CrackberryPi/hardware/Eagle/59440996.jpg

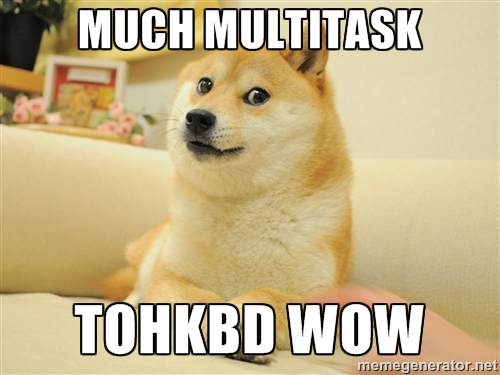
Eagle/59440996.jpg
