CrackberryPi/hardware/images/fotos/20150325_001.jpg

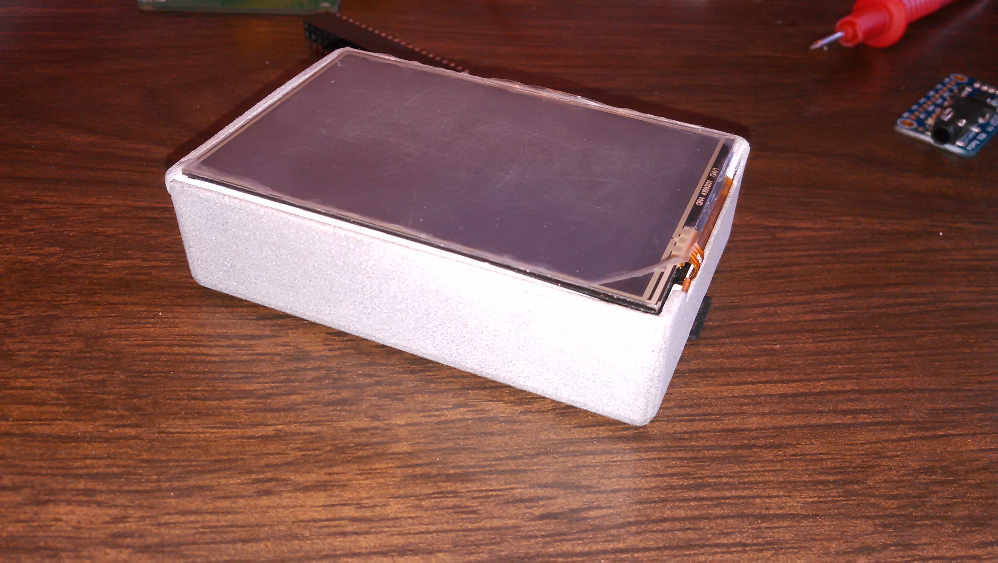
images/fotos/20150325_001.jpg
