CrackberryPi/hardware/images/fotos/20150325_002.jpg

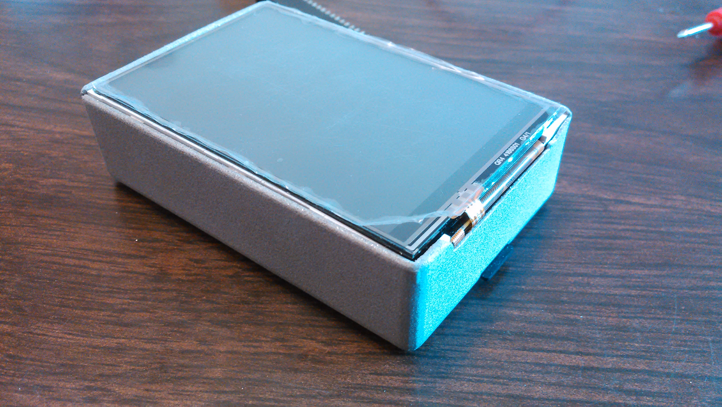
images/fotos/20150325_002.jpg
