CrackberryPi/hardware/images/fotos/20150325_003.jpg

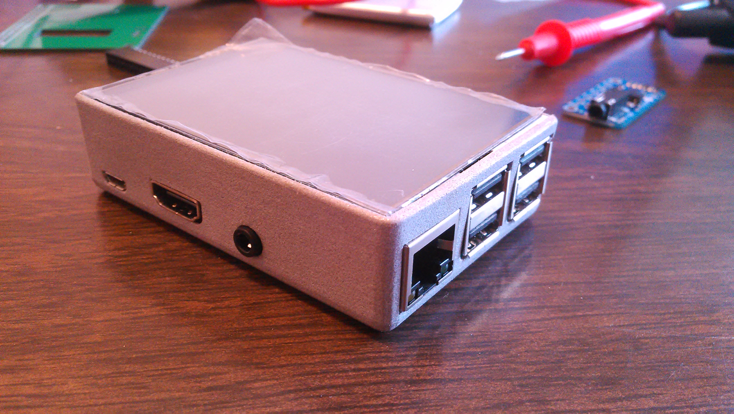
images/fotos/20150325_003.jpg
