CrackberryPi/hardware/images/fotos/20150325_004.jpg

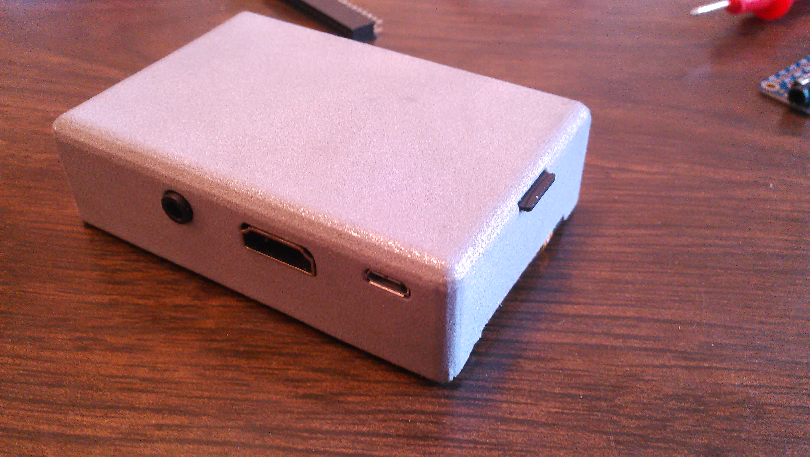
images/fotos/20150325_004.jpg
