CrackberryPi/hardware/images/fotos/20150325_005.jpg

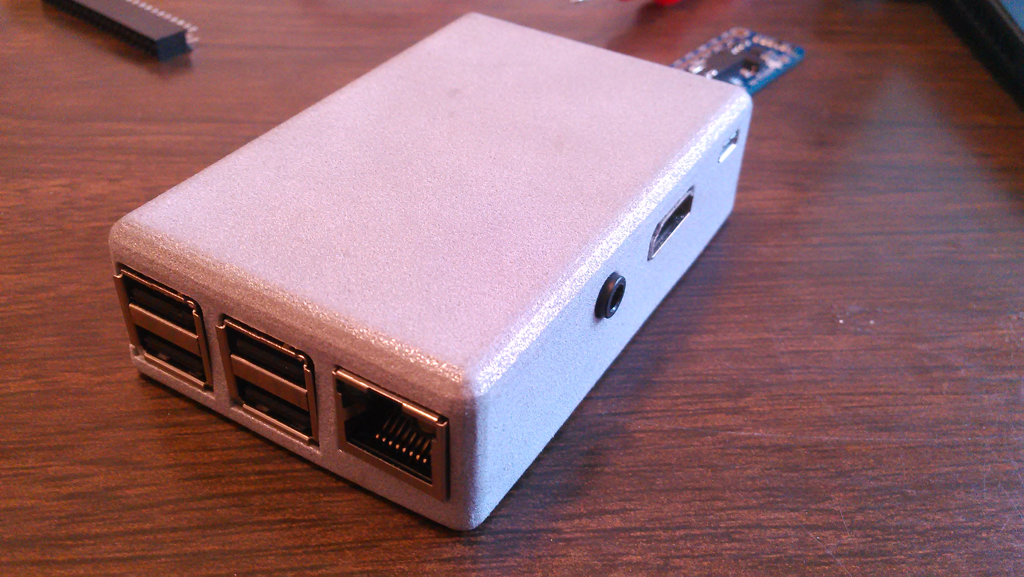
images/fotos/20150325_005.jpg
