CrackberryPi/hardware/images/fotos/20150325_006.jpg

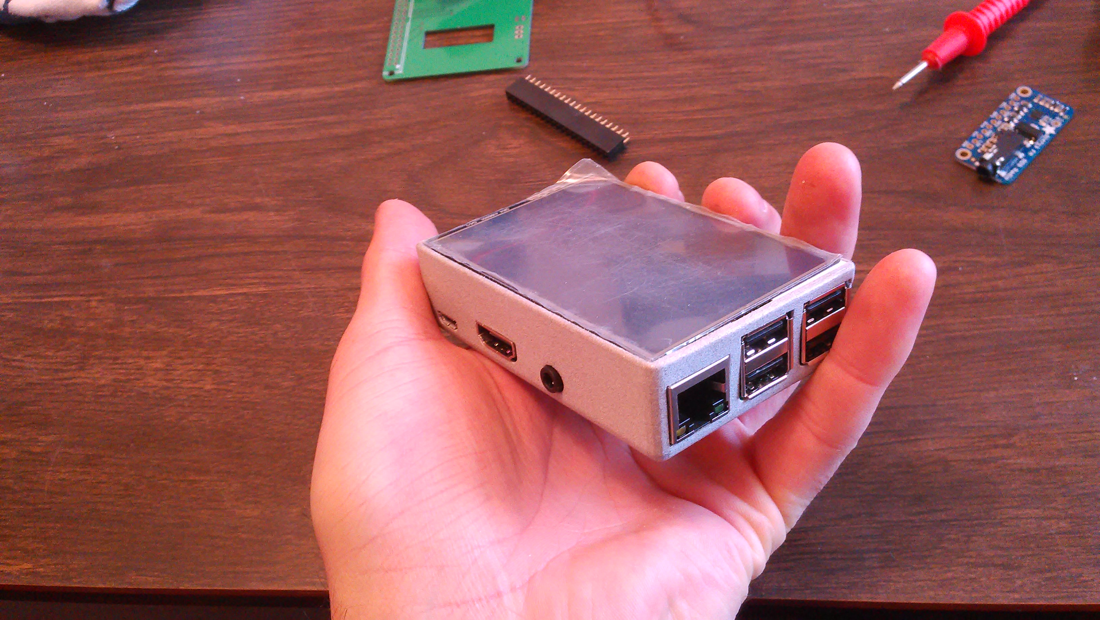
images/fotos/20150325_006.jpg
