CrackberryPi/hardware/images/fotos/20150325_007.jpg

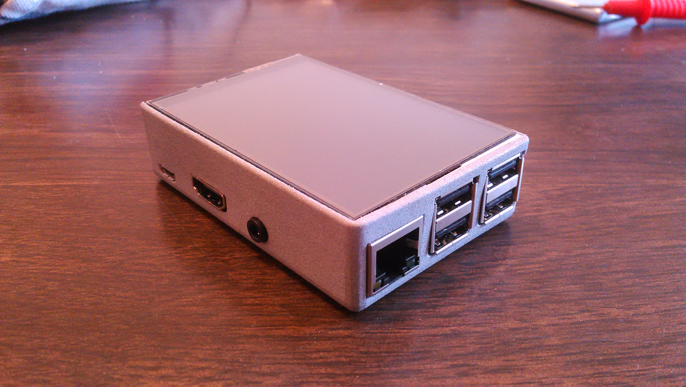
images/fotos/20150325_007.jpg
