CrackberryPi/hardware/images/fotos/20150325_008.jpg

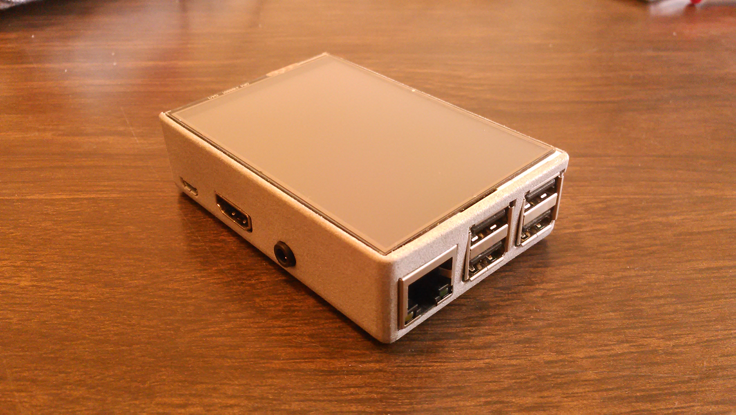
images/fotos/20150325_008.jpg
