CrackberryPi/hardware/images/fotos/20150325_009.jpg

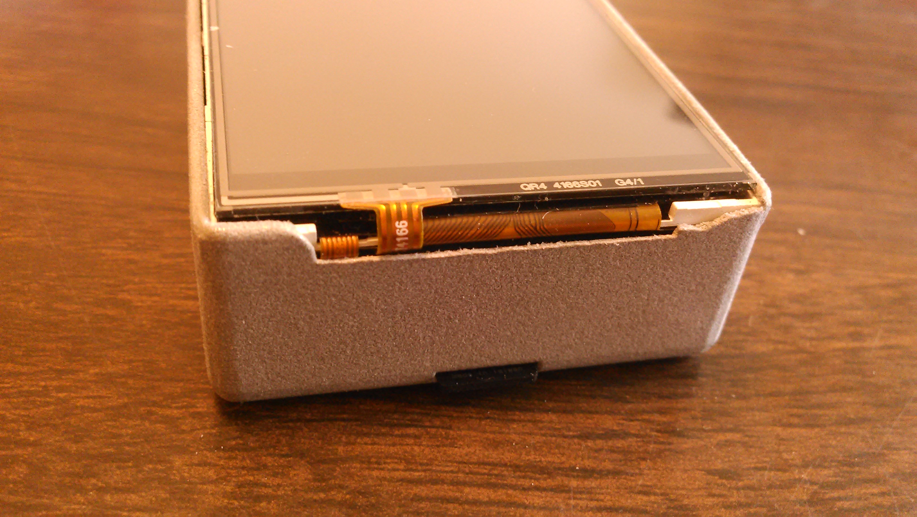
images/fotos/20150325_009.jpg
