CrackberryPi/hardware/images/kbd.jpg

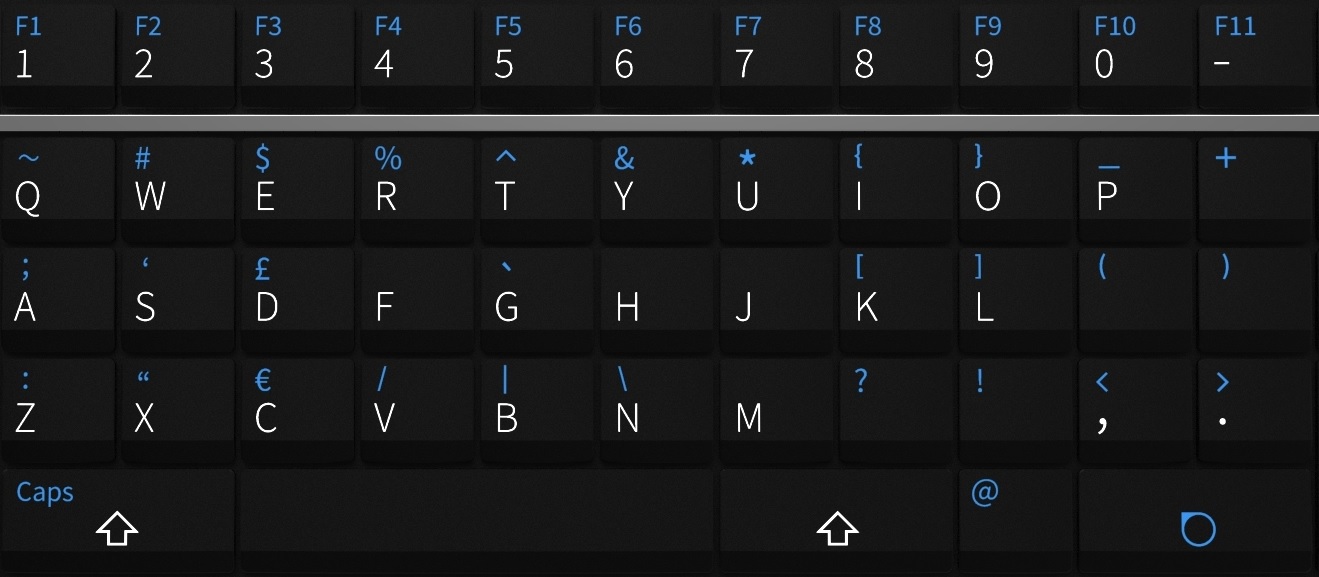
images/kbd.jpg
