CrackberryPi/hardware/images/raspbian.jpg

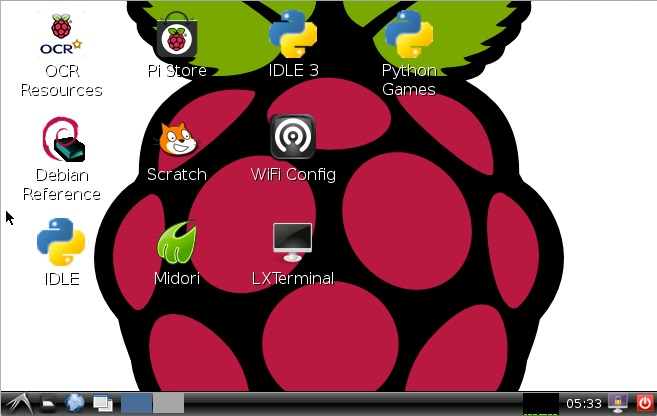
images/raspbian.jpg
