CrackberryPi/hardware/Eagle/CrackberryPi_1.0.5.brd

## EAGLE design Eagle/CrackberryPi_1.0.5.brd (2015-04-28)

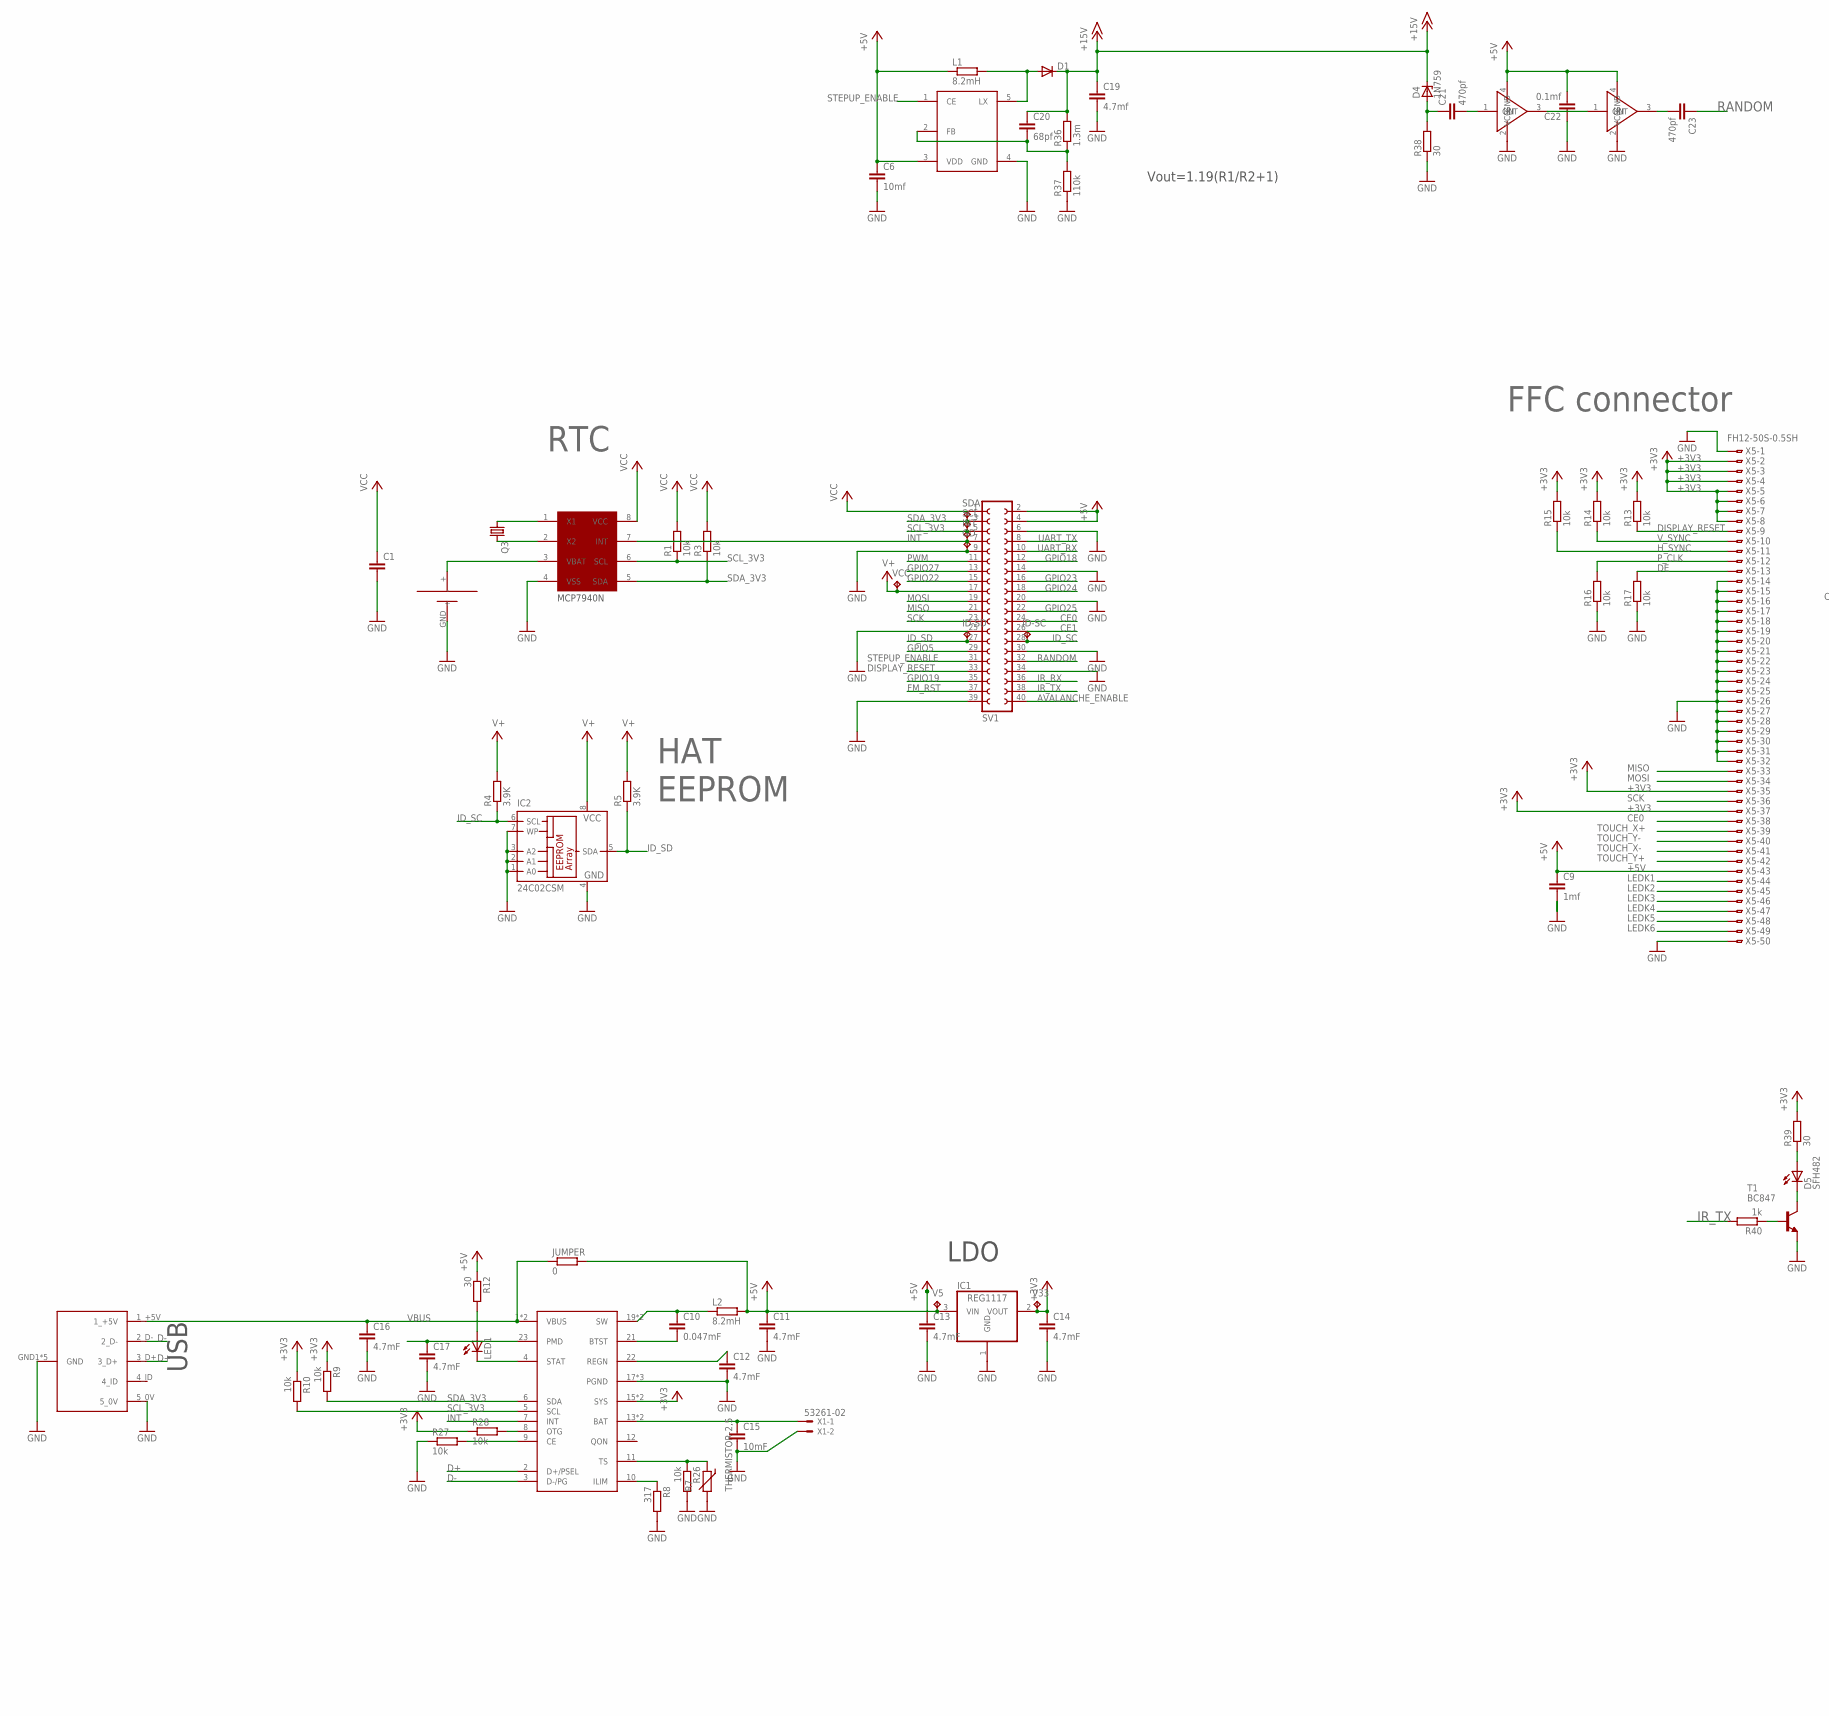
[picture p51: schematic CrackberryPi_1.0.5.sch, part in row 1, column 1]

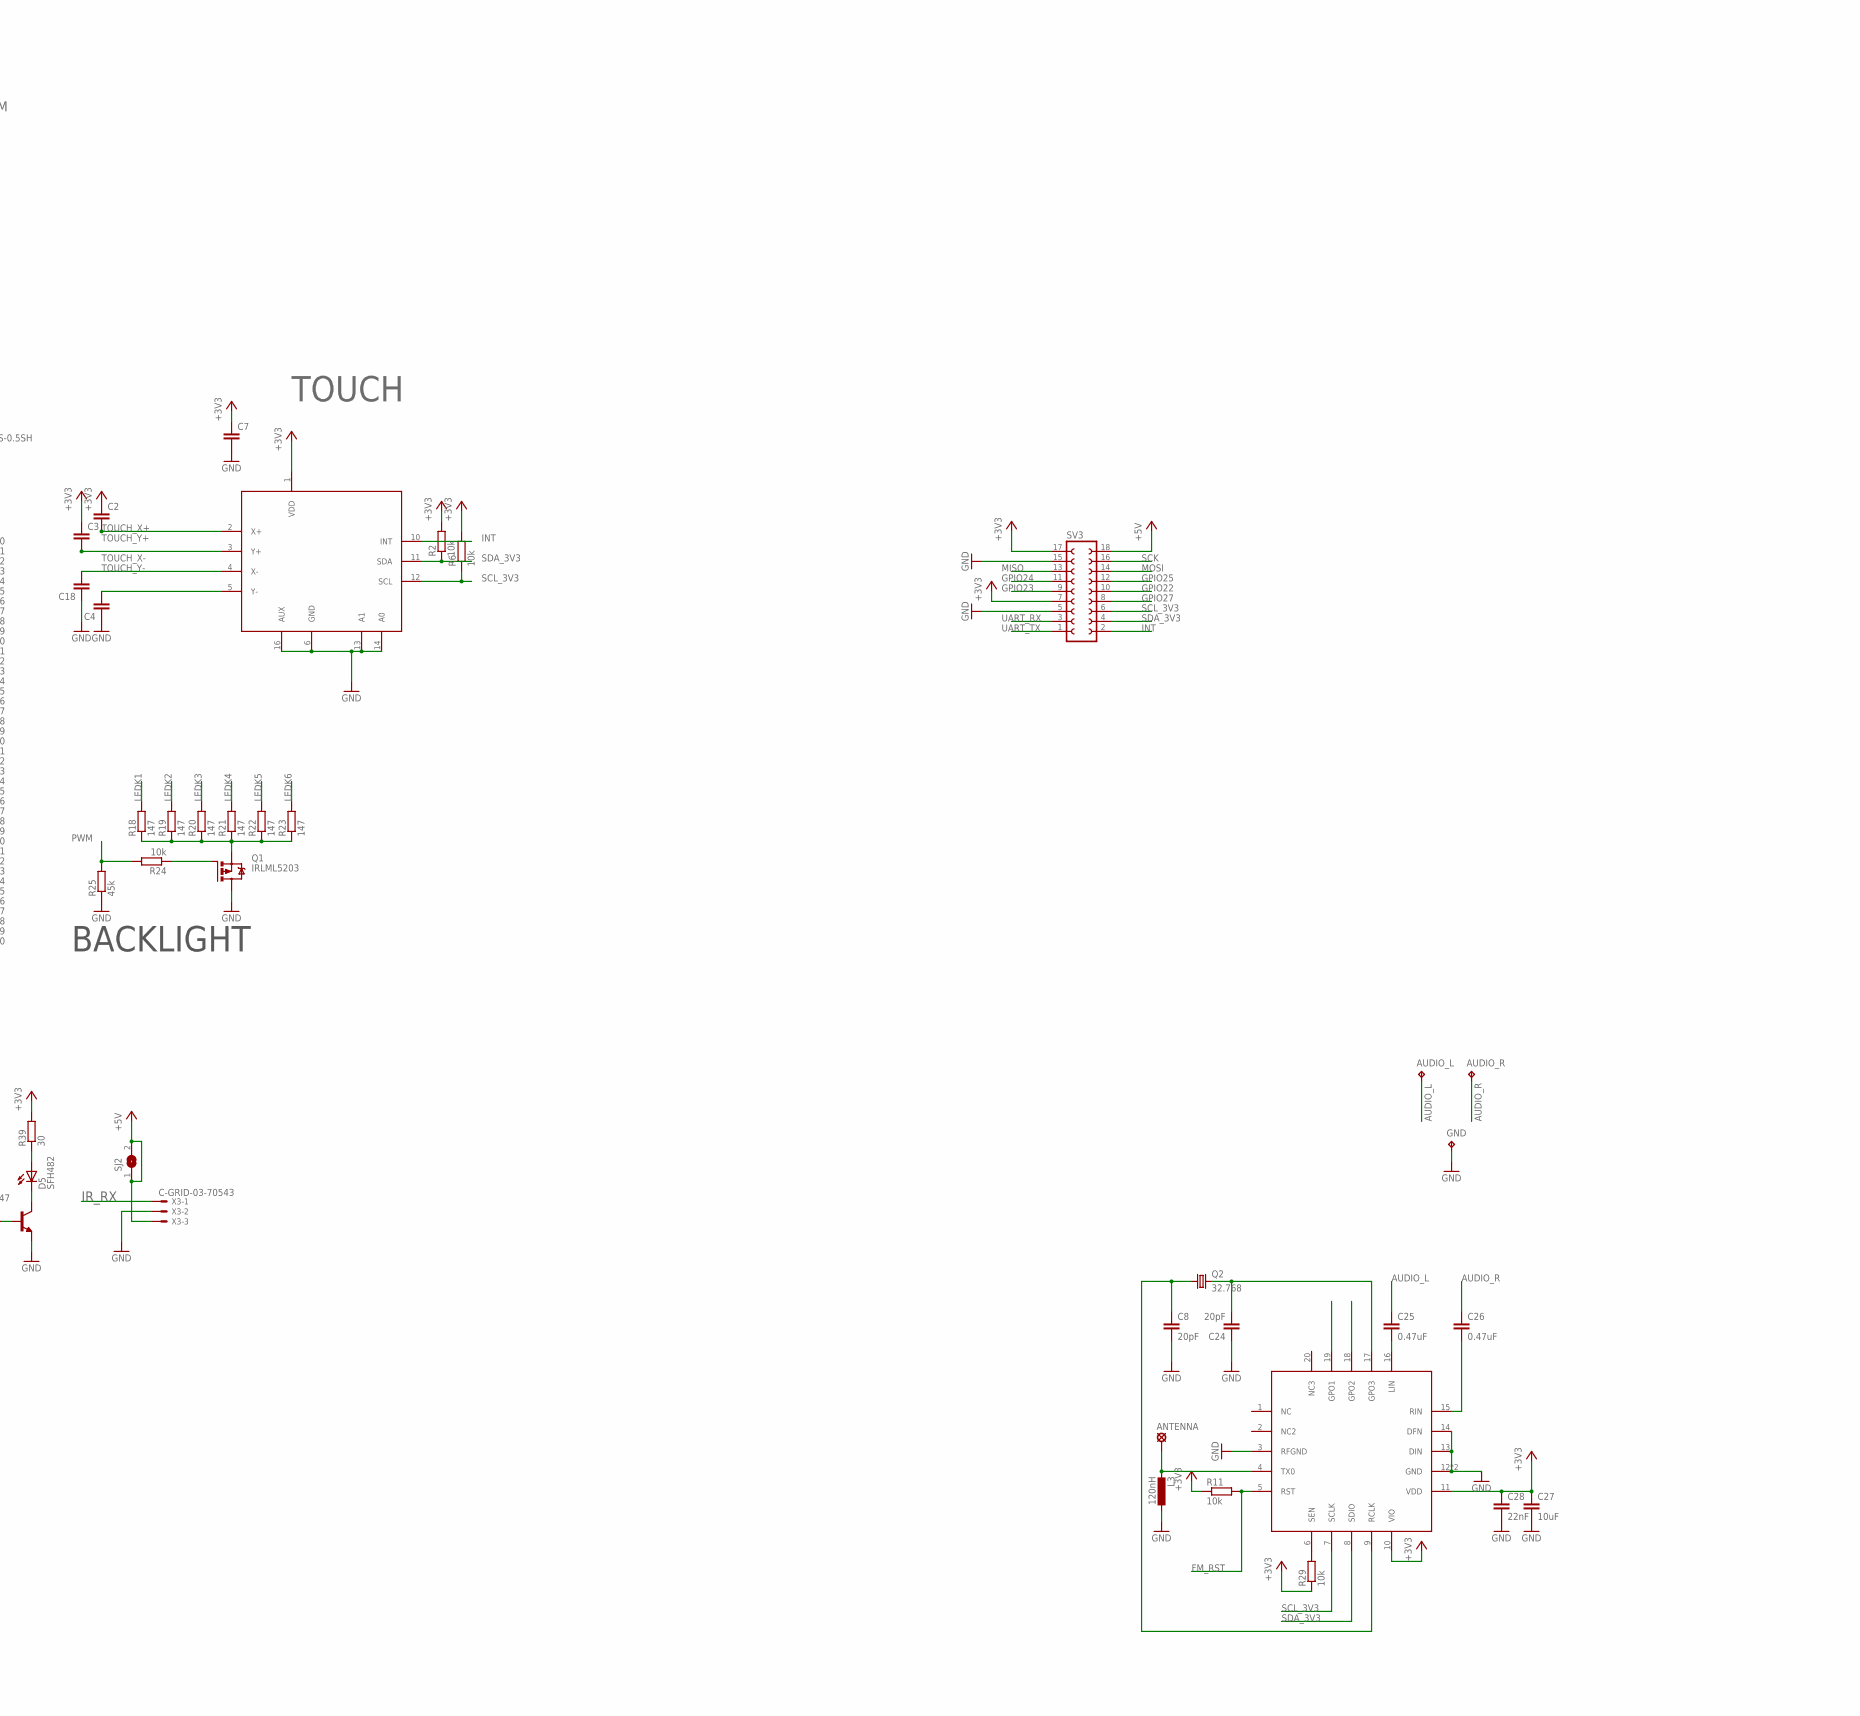
[picture p52: schematic CrackberryPi_1.0.5.sch, part in row 1, column 2]

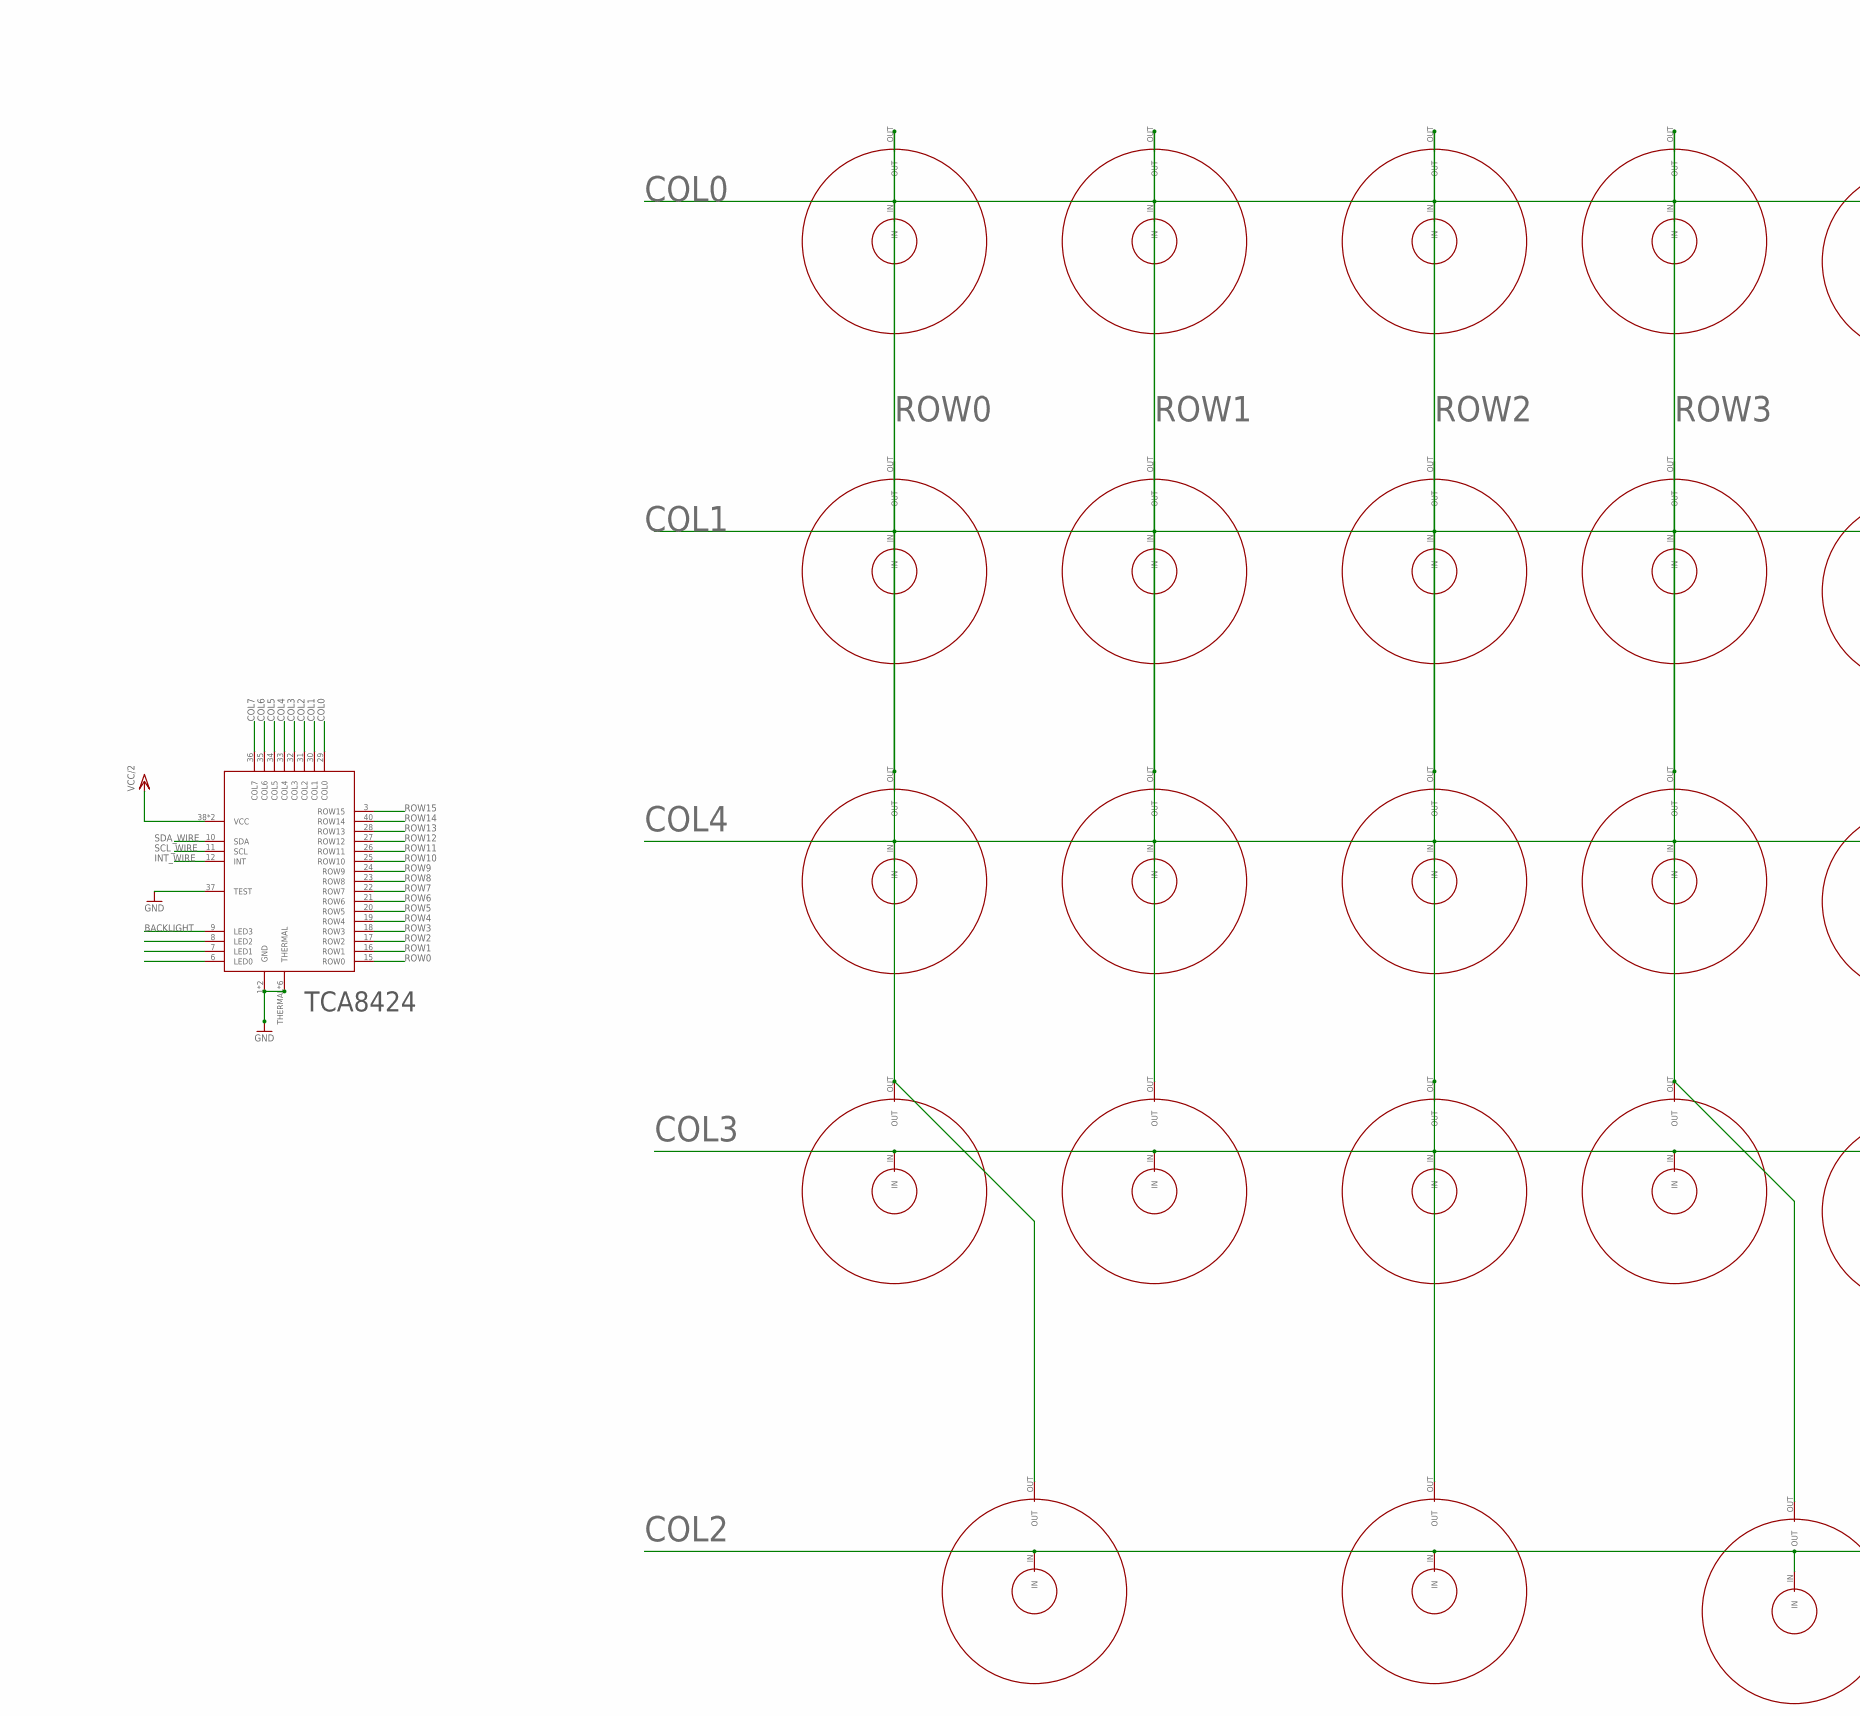
[picture p53: schematic CrackberryPi_1.0.5.sch, part in row 1, column 3]

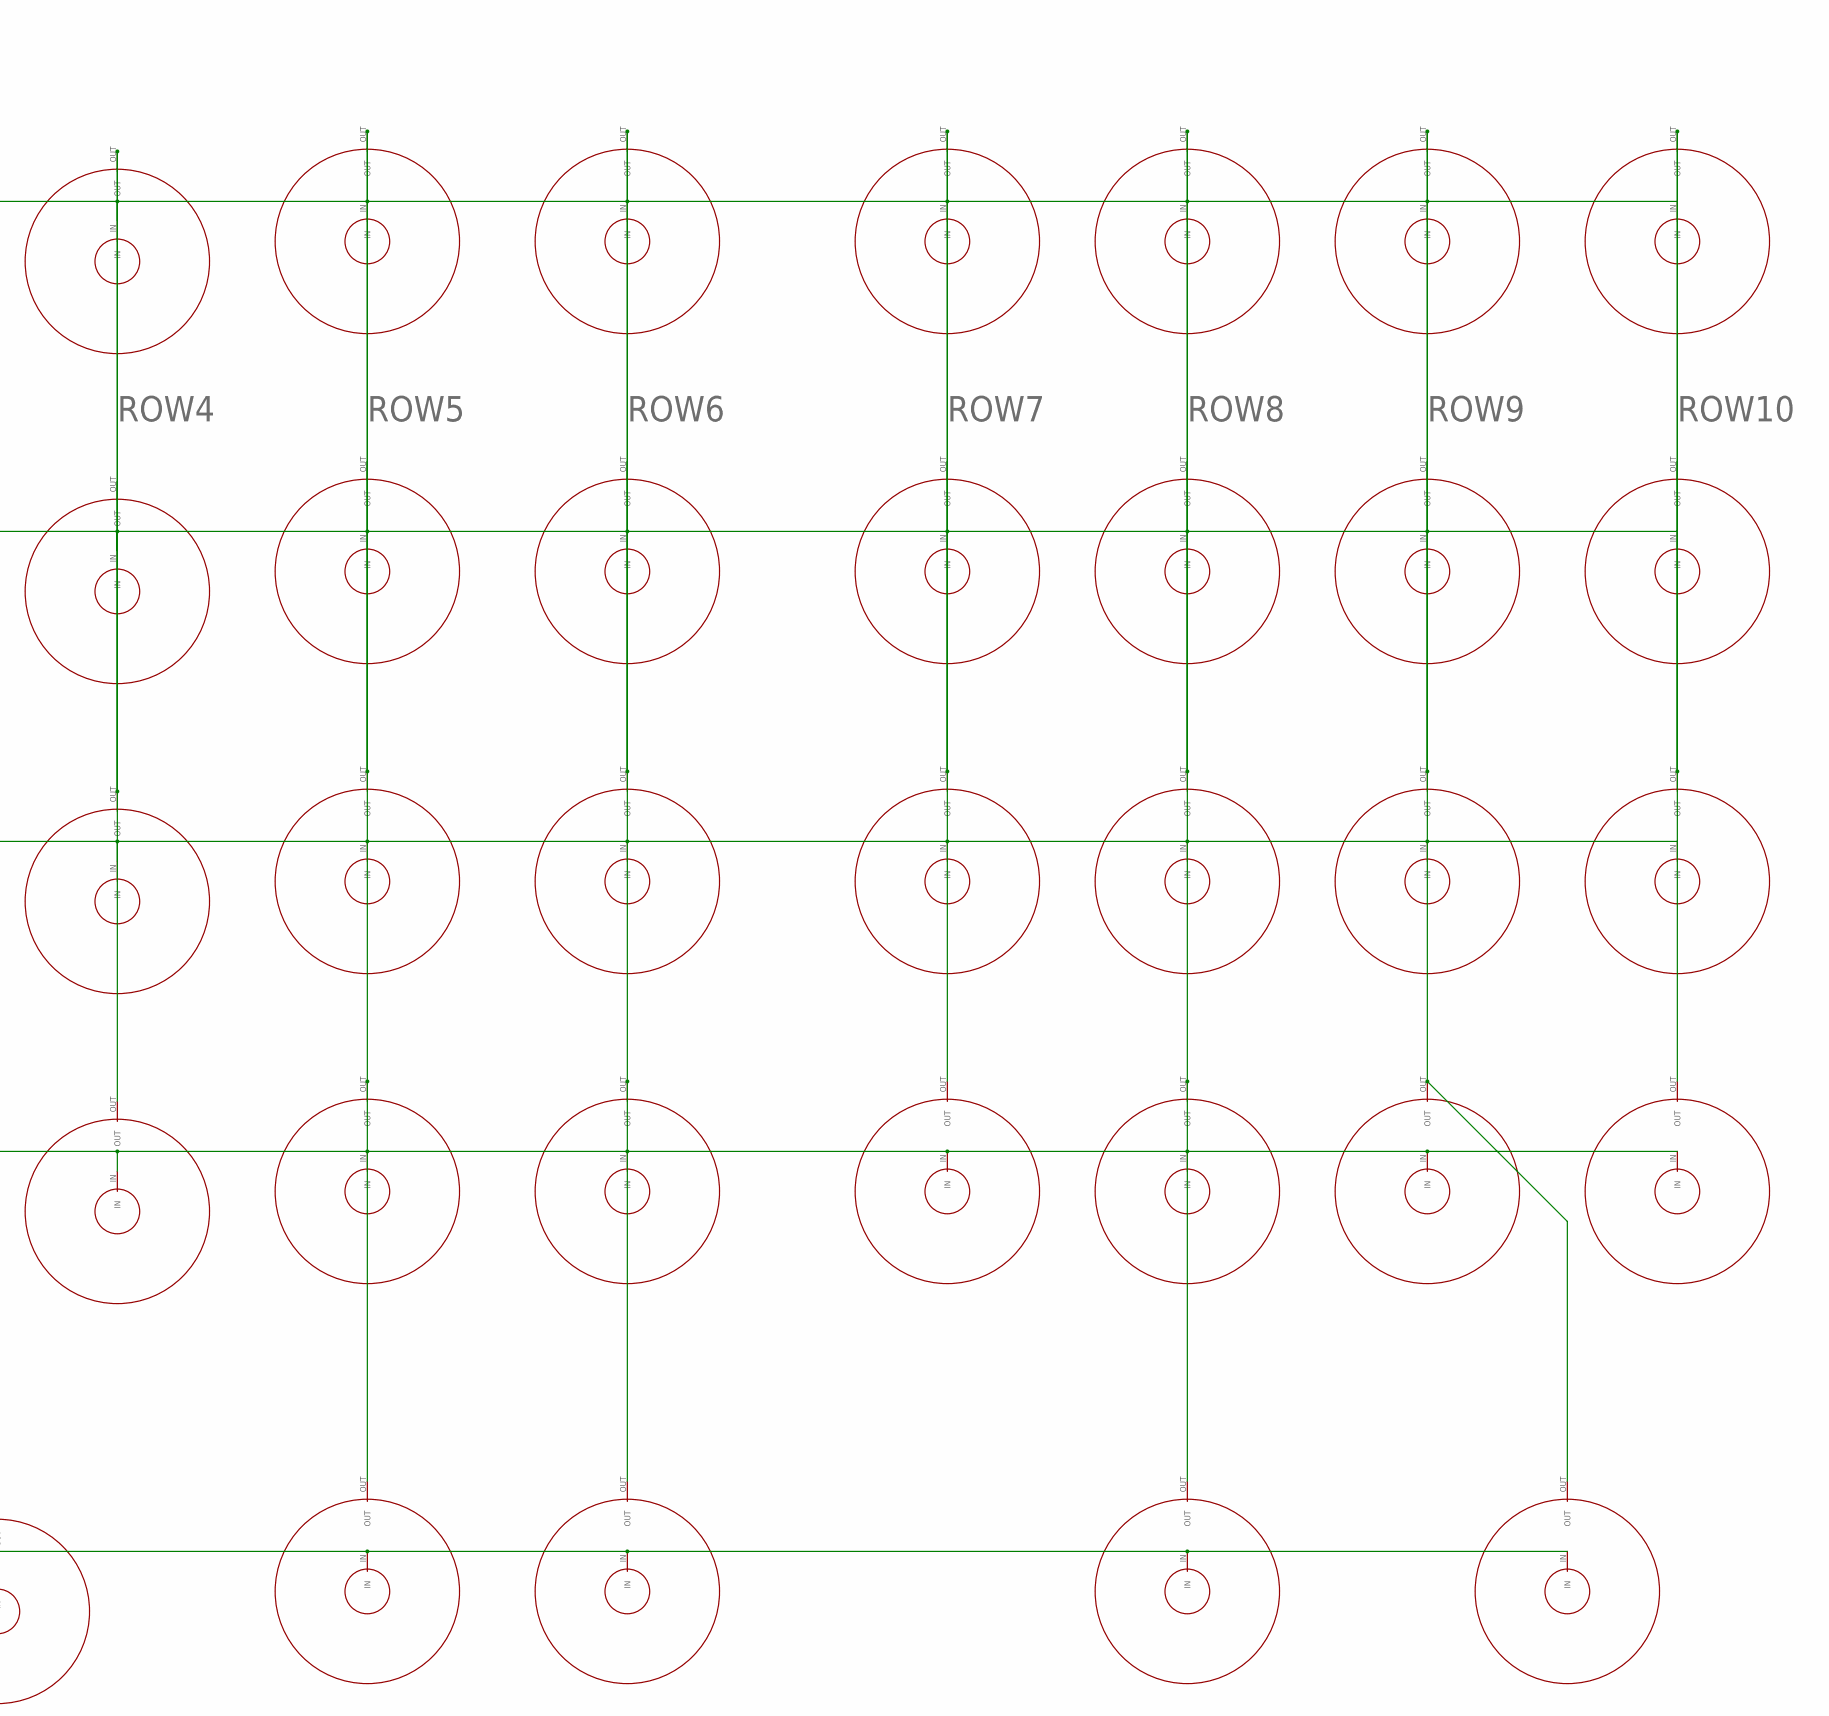
[picture p54: schematic CrackberryPi_1.0.5.sch, part in row 1, column 4]

Parts:
0, 1, 2, 3, 4, 5, 6, 7, 8, 9, .: DOME; 4MM
!: DOME; 4MM
(: DOME; 4MM
): DOME; 4MM
+: DOME; 4MM
,: DOME; 4MM
-: DOME; 4MM
?: DOME; 4MM
@: DOME; 4MM
A: DOME; 4MM
ANTENNA: LSP10
AUDIO_L: TPB2,54; B2,54
AUDIO_R: TPB2,54; B2,54
B: DOME; 4MM
C: DOME; 4MM
C1, C2, C3, C4, C7, C18: C-EUC0603; C0603
C6: 10mf; C0603
C8, C24: 20pF; C0603
C9: 1mf; C0603
C10: 0.047mF; C0402
C11, C12, C13, C14, C16, C17: 4.7mF; C0603
C15: 10mF; C1206
C19: 4.7mf; C0603
C20: 68pf; C0603
C21, C23: 470pf; C0603
C22: 0.1mf; C0603
C25, C26: 0.47uF; C0603
C27: 10uF; C0603
C28: 22nF; C0603
D: DOME; 4MM
D1: DIODE-SOD123; SOD123
D4: 1N759; SOD80C
D5: SFH482
E: DOME; 4MM
F: DOME; 4MM
FN-RIGHT: DOME; 4MM
G: DOME; 4MM
GD: TPB1,27; B1,27
GND: TPB2,54; B2,54
H: DOME; 4MM
I: DOME; 4MM
IC1: REG1117; SOT223
IC2: 24C02CSM; SO-08M
ID-SC: TPB1,27; B1,27
ID-SD: TPB1,27; B1,27
INT: TPB1,27; B1,27
J: DOME; 4MM
JUMPER: 0; R1206
K: DOME; 4MM
L: DOME; 4MM
L1: 8.2mH; R0805
L2: 8.2mH; R1206W
L3: 120nH; L2012C
LED1: LEDSML0603; SML0603
M: DOME; 4MM
N: DOME; 4MM
O: DOME; 4MM
P: DOME; 4MM
Q: DOME; 4MM
Q1: IRLML5203; MICRO3
Q2: 32.768; MM20SS
Q3: CRYSTALMM20SS; MM20SS
R: DOME; 4MM
R1, R2, R3, R6, R9, R10, R11, R13, R14, R15, R16, R17, R24, R26, R27, R28, R29: 10k; R0603
R4, R5: 3.9K; R0603
R7: THERMISTOR-2,5; RS-2,5
R8: 317; R0603
R12, R38, R39: 30; R0603
R18, R19, R20, R21, R22, R23: 147; R0603
R25: 45k; R0603
R36: 1.3m; R0603
R37: 110k; R0603
R40: 1k; R0603
S: DOME; 4MM
SCL: TPB1,27; B1,27
SDA: TPB1,27; B1,27
SHIFT-RIGHT: DOME; 4MM
SHILFT-LEFT: DOME; 4MM
SJ2: SJ
SPACE1, SPACE2, SPACE3: DOME; 4MM
SV1: FE20-2
SV3: FE09-2
T: DOME; 4MM
T1: BC847; SOT23
U: DOME; 4MM
U$1: BQ24297; VQFN-4X4-24
U$2: NCP1406; SOT23-5L
U$3, U$10: MAX2650; SOT143-W
U$4: CR1216
U$5: MCP7940N; SO08
U$6: TSC2007; TSSOP16
U$7: TCA8424; QFN40
U$8: SI4713; QFN20-3X3
U$9: MICRO_USB
V: DOME; 4MM
V5, V33: TPB1,27; B1,27
VCC: TPB1,27; B1,27
W: DOME; 4MM
X: DOME; 4MM
X1: 53261-02
X3: C-GRID-03-70543; 70543-03
X5: FH12-50S-0.5SH
Y: DOME; 4MM
Z: DOME; 4MM

Connections:
+3V3: C2.1, C3.1, C7.1, C14.1, C27.1, C28.1, IC1.2 (VOUT), R2.2, R6.2, R9.1, R10.1, R11.1, R13.2, R14.2, R15.2, R28.1, R29.1, R39.2, SV3.7, SV3.17, U$1.15 (SYS), U$1.16 (SYS), U$6.1 (VDD), U$8.10 (VIO), U$8.11 (VDD), V33.TP, X5.2, X5.3, X5.4, X5.5, X5.6, X5.7, X5.8, X5.35, X5.37
+5V: C6.1, C9.1, C11.1, C13.1, C22.2, IC1.3 (VIN), JUMPER.2, L1.1, L2.2, R12.1, SJ2.1, SJ2.2, SV1.2, SV1.4, SV3.18, U$2.3 (VDD), U$3.4 (VCC), U$10.4 (VCC), V5.TP, X3.3, X5.43
+15V: C19.1, C20.1, D1.C, D4.C, R36.2
AUDIO_L: AUDIO_L.TP, C25.1
AUDIO_R: AUDIO_R.TP, C26.1
AVALANCHE_ENABLE: SV1.40
BACKLIGHT: U$7.9 (LED3)
BASE: R40.1, T1.1 (B)
CE0: SV1.24, X5.38
CE1: SV1.26
COL0: 0.IN, 1.IN, 2.IN, 3.IN, 4.IN, 5.IN, 6.IN, 7.IN, 8.IN, 9.IN, -.IN, U$7.29 (COL0)
COL1: +.IN, E.IN, I.IN, O.IN, P.IN, Q.IN, R.IN, T.IN, U.IN, U$7.30 (COL1), W.IN, Y.IN
COL2: @.IN, FN-RIGHT.IN, SHIFT-RIGHT.IN, SHILFT-LEFT.IN, SPACE1.IN, SPACE2.IN, SPACE3.IN, U$7.31 (COL2)
COL3: !.IN, ,.IN, ..IN, ?.IN, B.IN, C.IN, M.IN, N.IN, U$7.32 (COL3), V.IN, X.IN, Z.IN
COL4: (.IN, ).IN, A.IN, D.IN, F.IN, G.IN, H.IN, J.IN, K.IN, L.IN, S.IN, U$7.33 (COL4)
COL5: U$7.34 (COL5)
COL6: U$7.35 (COL6)
COL7: U$7.36 (COL7)
COLLECTOR: D5.K (C), T1.3 (C)
D+: U$1.2 (D+/PSEL), U$9.3_D+
D-: U$1.3 (D-/PG), U$9.2_D-
DE: R17.2, X5.13
DISPLAY_RESET: R13.1, SV1.33, X5.9
EMITTER: T1.2 (E)
FB: C20.2, R36.1, R37.2, U$2.2 (FB)
FM_RST: R11.2, SV1.37, U$8.5 (RST)
GND: C1.2, C4.1, C6.2, C7.2, C8.2, C9.2, C11.2, C12.2, C13.2, C14.2, C15.2, C16.2, C17.2, C18.1, C19.2, C22.1, C24.1, C27.2, C28.2, GD.TP, GND.TP, IC1.1 (GND), IC2.1 (A0), IC2.2 (A1), IC2.3 (A2), IC2.4 (GND), IC2.7 (WP), L3.1, Q1.3 (D), R7.2, R8.2, R16.1, R17.1, R25.1, R26.2, R27.1, R37.1, R38.1, SV1.6, SV1.9, SV1.14, SV1.20, SV1.25, SV1.30, SV1.34, SV1.39, SV3.5, SV3.15, U$1.17 (PGND), U$1.18 (PGND), U$1.P$1 (PGND), U$2.4 (GND), U$3.2 (GND), U$4.GND (-), U$5.4 (VSS), U$6.6 (GND), U$6.13 (A1), U$6.14 (A0), U$6.16 (AUX), U$7.1 (GND), U$7.4 (GND), U$7.37 (TEST), U$7.THERMAL, U$7.VIA1 (THERMAL), U$7.VIA2 (THERMAL), U$7.VIA3 (THERMAL), U$7.VIA4 (THERMAL), U$7.VIA5 (THERMAL), U$8.3 (RFGND), U$8.12 (GND), U$8.13 (DIN), U$8.14 (DFN), U$8.P$1 (GND), U$9.5_0V, U$9.GND1 (GND), U$9.GND2 (GND), U$9.GND5 (GND), U$9.P$1 (GND), U$9.P$7 (GND), U$10.2 (GND), X1.2, X3.2, X5.1, X5.14, X5.15, X5.16, X5.17, X5.18, X5.19, X5.20, X5.21, X5.22, X5.23, X5.24, X5.25, X5.26, X5.27, X5.28, X5.29, X5.30, X5.31, X5.32, X5.50
GPIO5: SV1.29
GPIO18: SV1.12
GPIO19: SV1.35
GPIO22: SV1.15, SV3.10
GPIO23: SV1.16, SV3.9
GPIO24: SV1.18, SV3.11
GPIO25: SV1.22, SV3.12
GPIO27: SV1.13, SV3.8
GPO1: U$8.19 (GPO1)
GPO2: U$8.18 (GPO2)
H_SYNC: R15.1, X5.11
ID_SC: IC2.6 (SCL), ID-SC.TP, R4.1, SV1.28
ID_SD: IC2.5 (SDA), ID-SD.TP, R5.1, SV1.27
INT: INT.TP, SV1.7, SV3.2, U$1.7 (INT), U$5.7 (INT), U$6.10 (INT)
INT_WIRE: U$7.12 (INT)
IN_1: C21.2, U$3.1 (IN)
IR_RX: SV1.36, X3.1
IR_TX: R40.2, SV1.38
LEDK1: R18.2, X5.44
LEDK2: R19.2, X5.45
LEDK3: R20.2, X5.46
LEDK4: R21.2, X5.47
LEDK5: R22.2, X5.48
LEDK6: R23.2, X5.49
LX: D1.A, L1.2, U$2.5 (LX)
MISO: SV1.21, SV3.13, X5.33
MOSI: SV1.19, SV3.14, X5.34
unnamed: C10.1, L2.1, U$1.19 (SW), U$1.20 (SW)
unnamed: C10.2, U$1.21 (BTST)
unnamed: C15.1, U$1.13 (BAT), U$1.14 (BAT), X1.1
unnamed: LED1.A, R12.2
unnamed: C12.1, U$1.22 (REGN)
unnamed: R7.1, R26.1, U$1.11 (TS)
unnamed: R8.1, U$1.10 (ILIM)
unnamed: C17.1, U$1.23 (PMD)
unnamed: LED1.C, U$1.4 (STAT)
unnamed: Q3.1, U$5.1 (X1)
unnamed: Q1.2 (S), R18.1, R19.1, R20.1, R21.1, R22.1, R23.1
unnamed: Q3.4 (2), U$5.2 (X2)
unnamed: R27.2, U$1.9 (CE)
unnamed: C21.1, D4.A, R38.2
unnamed: R28.2, U$1.8 (OTG)
unnamed: C24.2, Q2.4 (2), U$8.17 (GPO3)
unnamed: Q1.1 (G), R24.1
unnamed: C8.1, Q2.1, U$8.9 (RCLK)
unnamed: C25.2, U$8.16 (LIN)
unnamed: C26.2, U$8.15 (RIN)
unnamed: ANTENNA.MP, L3.2, U$8.4 (TX0)
unnamed: R29.2, U$8.6 (SEN)
unnamed: D5.A, R39.1
OUT1_IN2: U$3.3 (OUT), U$10.1 (IN)
OUT2: C23.2, U$10.3 (OUT)
PWM: R24.2, R25.2, SV1.11
P_CLK: R16.2, X5.12
RANDOM: C23.1, SV1.32
ROW0: 1.OUT, A.OUT, Q.OUT, SHILFT-LEFT.OUT, U$7.15 (ROW0), Z.OUT
ROW1: 2.OUT, S.OUT, U$7.16 (ROW1), W.OUT, X.OUT
ROW2: 3.OUT, C.OUT, D.OUT, E.OUT, SPACE1.OUT, U$7.17 (ROW2)
ROW3: 4.OUT, F.OUT, R.OUT, SPACE2.OUT, U$7.18 (ROW3), V.OUT
ROW4: 5.OUT, B.OUT, G.OUT, T.OUT, U$7.19 (ROW4)
ROW5: 6.OUT, H.OUT, N.OUT, SPACE3.OUT, U$7.20 (ROW5), Y.OUT
ROW6: 7.OUT, J.OUT, M.OUT, SHIFT-RIGHT.OUT, U.OUT, U$7.21 (ROW6)
ROW7: 8.OUT, ?.OUT, I.OUT, K.OUT, U$7.22 (ROW7)
ROW8: 9.OUT, !.OUT, @.OUT, L.OUT, O.OUT, U$7.23 (ROW8)
ROW9: 0.OUT, (.OUT, ,.OUT, FN-RIGHT.OUT, P.OUT, U$7.24 (ROW9)
ROW10: ).OUT, +.OUT, -.OUT, ..OUT, U$7.25 (ROW10)
ROW11: U$7.26 (ROW11)
ROW12: U$7.27 (ROW12)
ROW13: U$7.28 (ROW13)
ROW14: U$7.40 (ROW14)
ROW15: U$7.3 (ROW15)
SCK: SV1.23, SV3.16, X5.36
SCL_3V3: R1.1, R6.1, R10.2, SCL.TP, SV1.5, SV3.6, U$1.5 (SCL), U$5.6 (SCL), U$6.12 (SCL), U$8.7 (SCLK)
SCL_WIRE: U$7.11 (SCL)
SDA_3V3: R2.1, R3.1, R9.2, SDA.TP, SV1.3, SV3.4, U$1.6 (SDA), U$5.5 (SDA), U$6.11 (SDA), U$8.8 (SDIO)
SDA_WIRE: U$7.10 (SDA)
STEPUP_ENABLE: SV1.31, U$2.1 (CE)
TOUCH_X+: C2.2, U$6.2 (X+), X5.39
TOUCH_X-: C18.2, U$6.4 (X-), X5.41
TOUCH_Y+: C3.2, U$6.3 (Y+), X5.42
TOUCH_Y-: C4.2, U$6.5 (Y-), X5.40
UART_RX: SV1.10, SV3.3
UART_TX: SV1.8, SV3.1
V+: IC2.8 (VCC), R4.2, R5.2, SV1.17, VCC.TP
VBAT+: U$4.+, U$5.3 (VBAT)
VBUS: C16.1, JUMPER.1, U$1.1 (VBUS), U$1.24 (VBUS), U$9.1_+5V
VCC: C1.1, R1.2, R3.2, SV1.1, U$5.8 (VCC)
VCC/2: U$7.38 (VCC), U$7.39 (VCC)
V_SYNC: R14.1, X5.10

Notes on the sheet:
RTC
HAT EEPROM
TOUCH
FFC connector
BACKLIGHT
MCP7940N
USB
LDO
Vout=1.19(R1/R2+1)
TCA8424

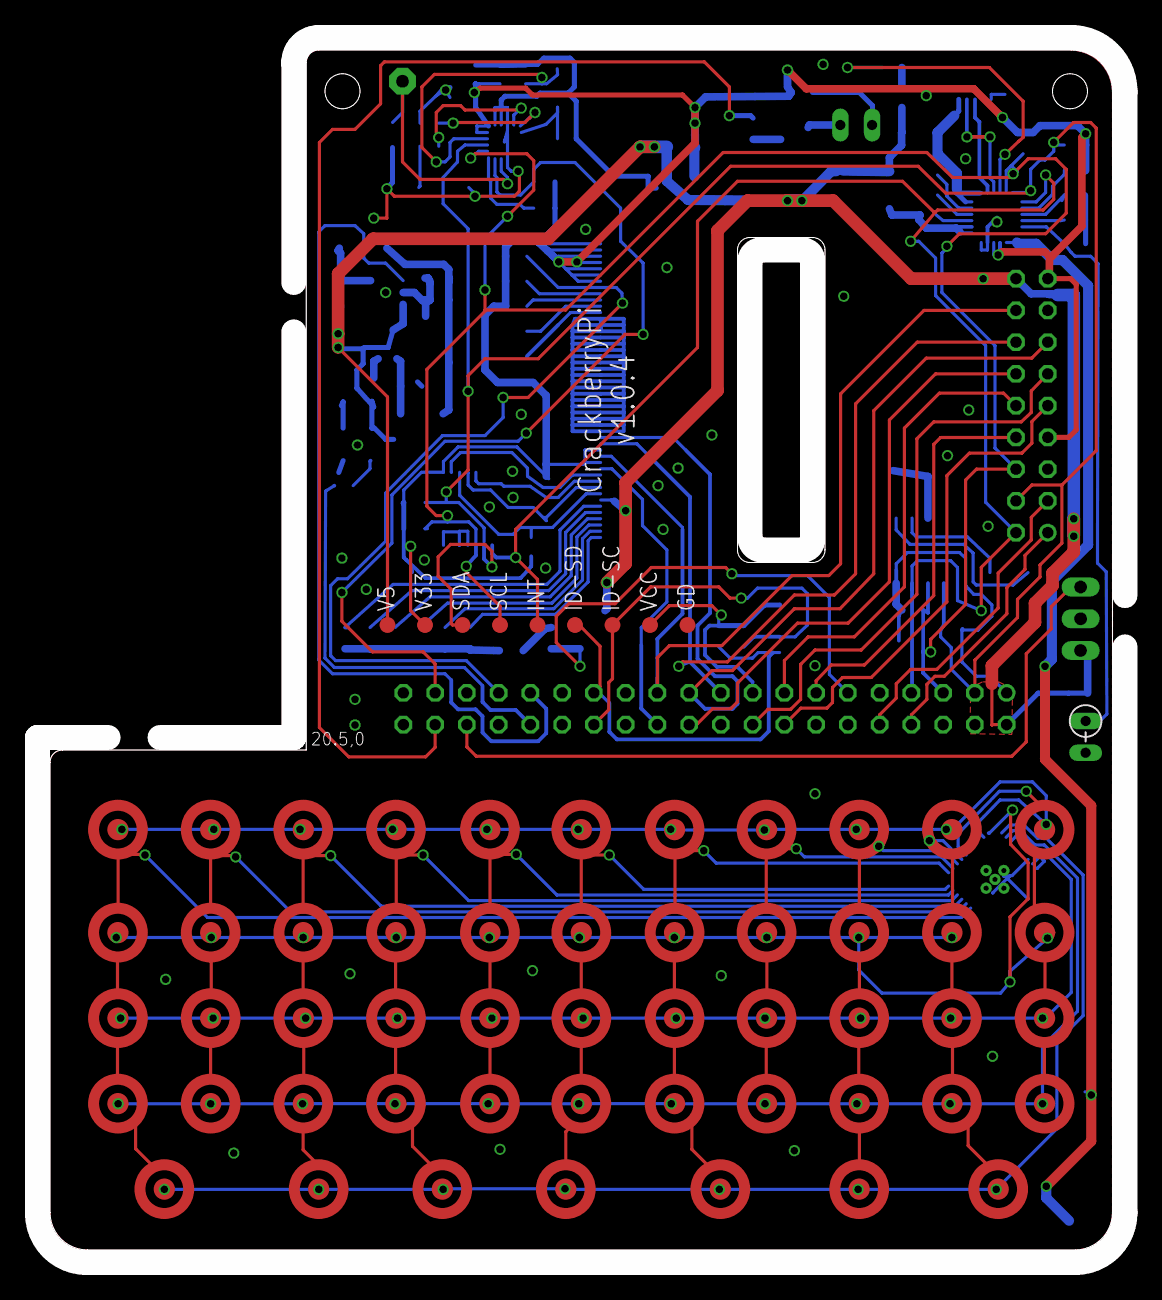
[picture p55: board CrackberryPi_1.0.5.brd from above]

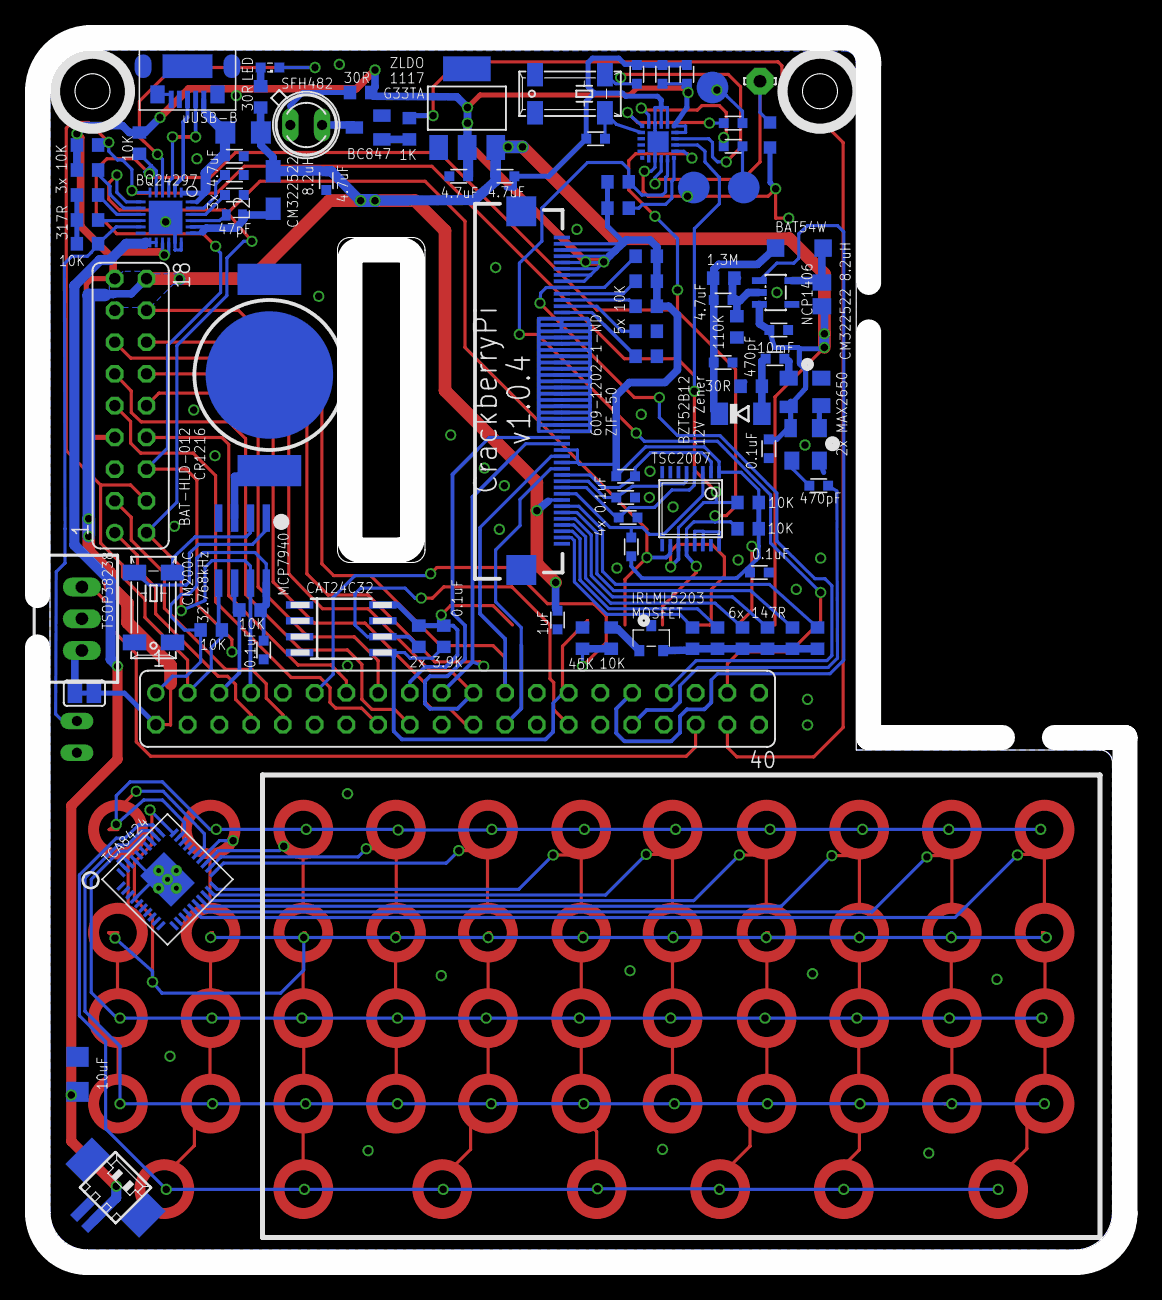
[picture p56: board CrackberryPi_1.0.5.brd from below]

Board: 2 copper layers, 87.0 x 98.0 mm, 155 parts (94 on the bottom side), 96 nets.
